jardelufc/Esperanto/software/src/include/engels.h

/*
   Por Jardel Silveira (jardel.silveira@engelsolutions.com.br)
   Lib MDB para coin changer
   Criada em 12 de março de 2007
*/

#ifndef __ENGELS_H
#define __ENGELS_H

typedef  unsigned char BYTE;
typedef  unsigned long DWORD;
typedef  unsigned short WORD;

#define BIT0 0x01
#define BIT1 0x02
#define BIT2 0x04
#define BIT3 0x08
#define BIT4 0x10
#define BIT5 0x20
#define BIT6 0x40
#define BIT7 0x80

#define LEDLIB

#endif
